its-succ/dakoku-board/esp8266_mqtt.h

/******************************************************************************
 * Copyright 2018 Google
 * Licensed under the Apache License, Version 2.0 (the "License");
 * you may not use this file except in compliance with the License.
 * You may obtain a copy of the License at
 *
 *    http://www.apache.org/licenses/LICENSE-2.0
 *
 * Unless required by applicable law or agreed to in writing, software
 * distributed under the License is distributed on an "AS IS" BASIS,
 * WITHOUT WARRANTIES OR CONDITIONS OF ANY KIND, either express or implied.
 * See the License for the specific language governing permissions and
 * limitations under the License.
 *****************************************************************************/
// This file contains static methods for API requests using Wifi / MQTT
#ifndef __ESP8266_MQTT_H__
#define __ESP8266_MQTT_H__
#include <ESP8266WiFi.h>
#include "FS.h"
#include <WiFiClientSecure.h>
#include <time.h>

#include <MQTT.h>

#include <CloudIoTCore.h>
#include <CloudIoTCoreMqtt.h>
#include "ciotc_config.h" // Wifi configuration here

// !!REPLACEME!!
// The MQTT callback function for commands and configuration updates
// Place your message handler code here.
void messageReceived(String &topic, String &payload) {
  Serial.println("incoming: " + topic + " - " + payload);
}
///////////////////////////////

// Initialize WiFi and MQTT for this board
MQTTClient *mqttClient;
Client *netClient;
CloudIoTCoreDevice *device;
CloudIoTCoreMqtt *mqtt;
unsigned long iss = 0;
String jwt;

///////////////////////////////
// Helpers specific to this board
///////////////////////////////
String getJwt() {
  // Disable software watchdog as these operations can take a while.
  ESP.wdtDisable();
  iss = time(nullptr);
  Serial.println("Refreshing JWT");
  jwt = device->createJWT(iss, jwt_exp_secs);
  ESP.wdtEnable(0);
  return jwt;
}

void setupCert() {
  // Set CA cert on wifi client
  // If using a static (binary) cert, uncomment in ciotc_config.h:
  ((WiFiClientSecure*)netClient)->setCACert_P(ca_crt, ca_crt_len);
  return;
}

///////////////////////////////
// Orchestrates various methods from preceeding code.
///////////////////////////////
void publishTelemetry(String data) {
  Serial.println(data);
  mqtt->publishTelemetry(data);
  mqtt->logReturnCode();
  mqtt->logError();
}

void publishTelemetry(String subfolder, String data) {
  mqtt->publishTelemetry(subfolder, data);
}

void connect() {
  mqtt->mqttConnect();
}

// TODO: fix globals
void setupCloudIoT() {
  // Create the device
  device = new CloudIoTCoreDevice(
      project_id, location, registry_id, device_id,
      private_key_str);

  // ESP8266 WiFi secure initialization
  setupCert();

  mqttClient = new MQTTClient(512);
  mqttClient->setOptions(180, true, 1000); // keepAlive, cleanSession, timeout
  mqtt = new CloudIoTCoreMqtt(mqttClient, netClient, device);
  mqtt->setLogConnect(true);
  mqtt->startMQTT(); // Opens connection
}

#endif //__ESP8266_MQTT_H__
